ethmacc/CASA0021_GroupPrototypingPitch/Media/cardboard_prototype_1.jpg

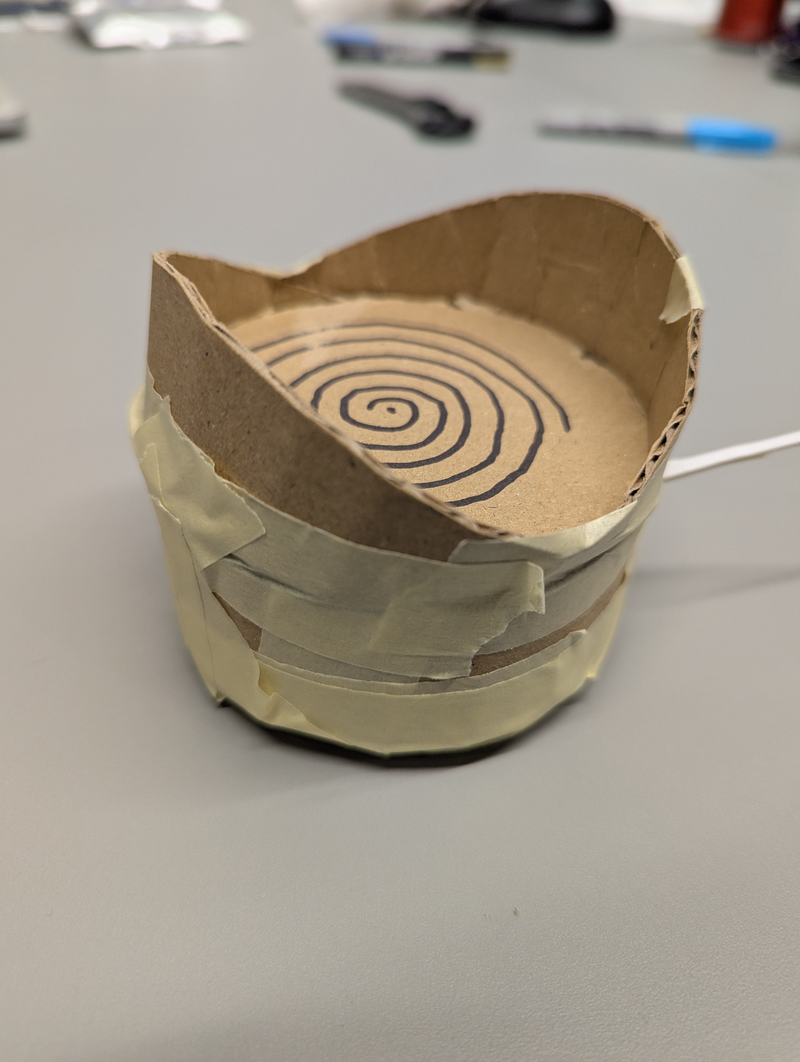
Media/cardboard_prototype_1.jpg
