ethmacc/CASA0021_GroupPrototypingPitch/Media/device_pair_1.jpg

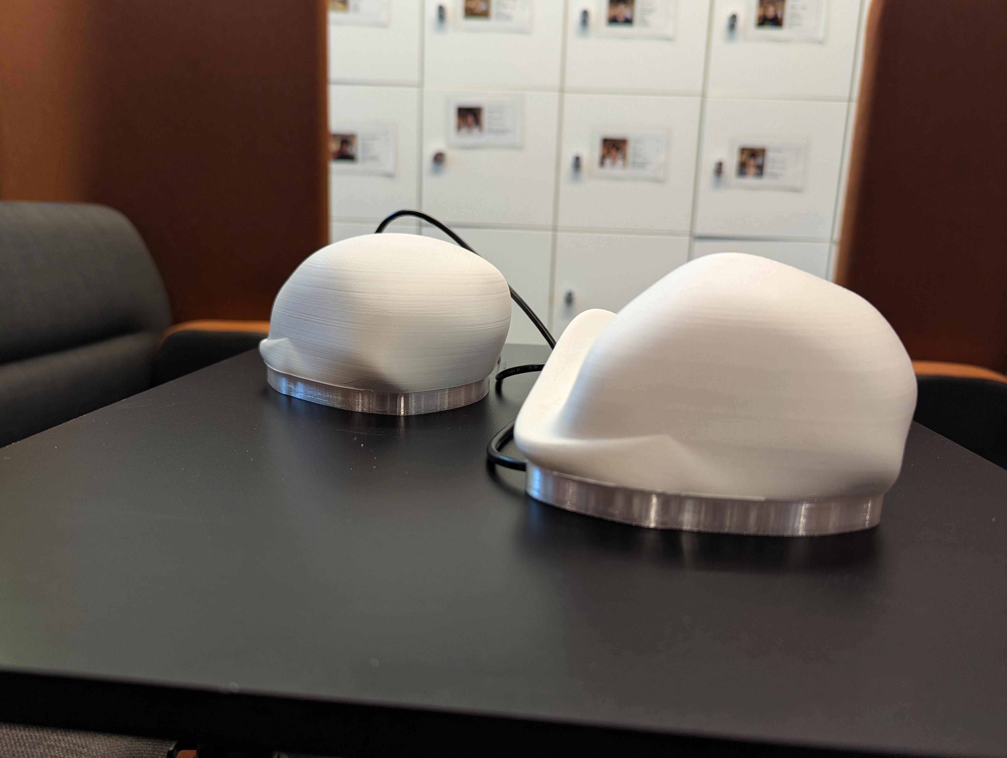
Media/device_pair_1.jpg
