ethmacc/CASA0021_GroupPrototypingPitch/Media/early_form_sketch.jpeg

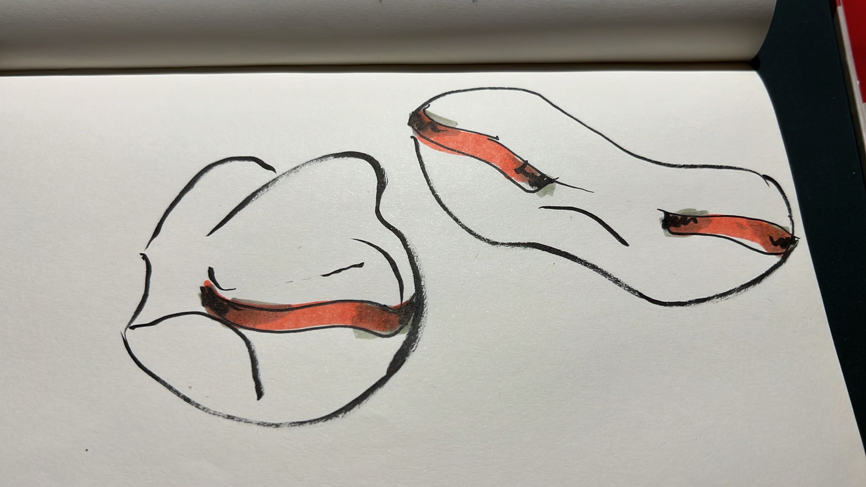
Media/early_form_sketch.jpeg
