ethmacc/CASA0021_GroupPrototypingPitch/Media/early_moon_sketch.jpeg

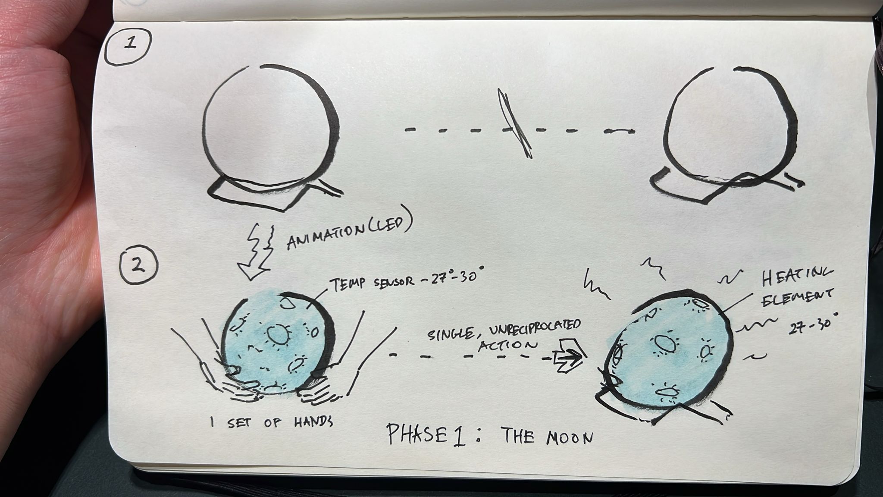
Media/early_moon_sketch.jpeg
