ethmacc/CASA0021_GroupPrototypingPitch/Media/early_sun_sketch.jpeg

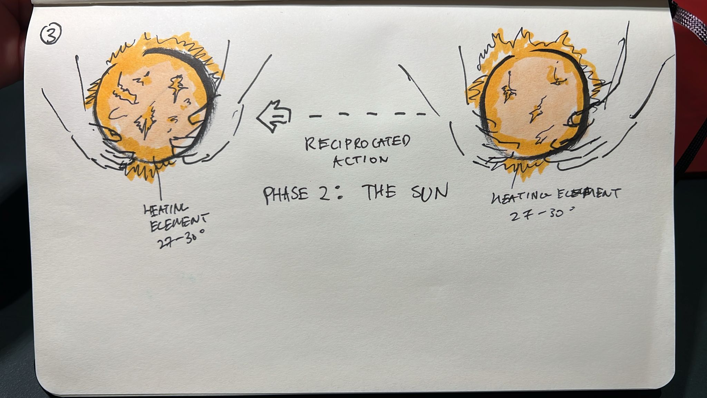
Media/early_sun_sketch.jpeg
