ethmacc/CASA0021_GroupPrototypingPitch/Media/early_watch_sketch.jpeg

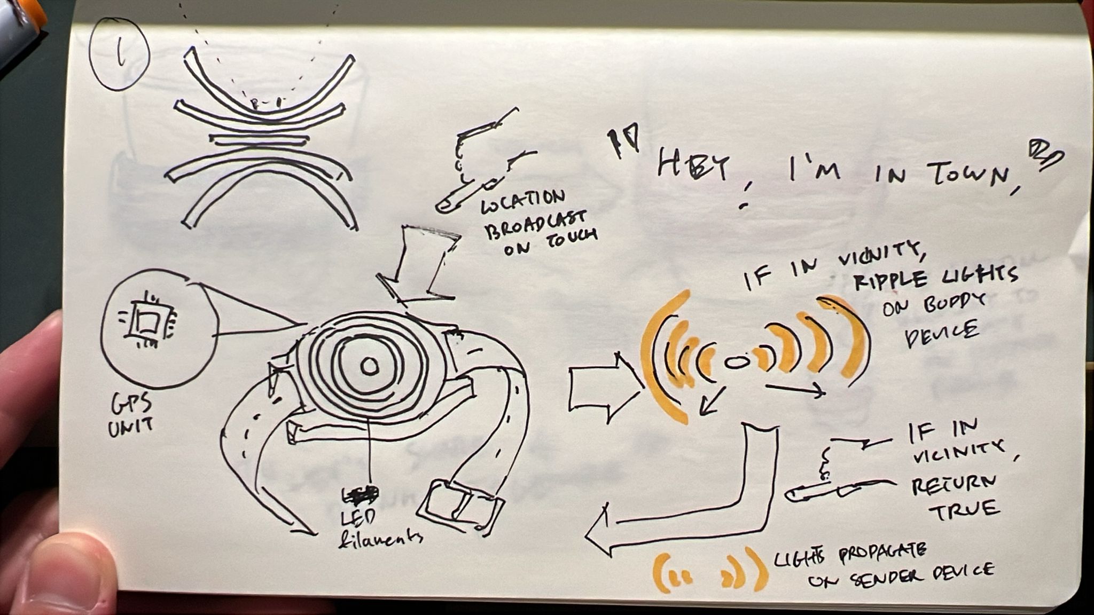
Media/early_watch_sketch.jpeg
