ethmacc/CASA0021_GroupPrototypingPitch/Media/electrical_diagram_1.jpeg

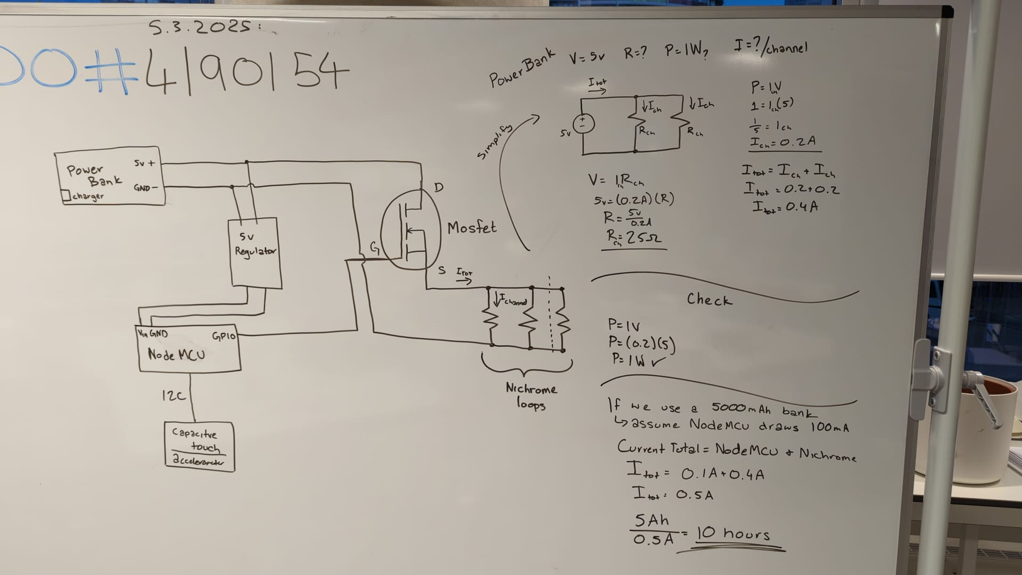
Media/electrical_diagram_1.jpeg
