ethmacc/CASA0021_GroupPrototypingPitch/Media/electrical_diagram_2.jpeg

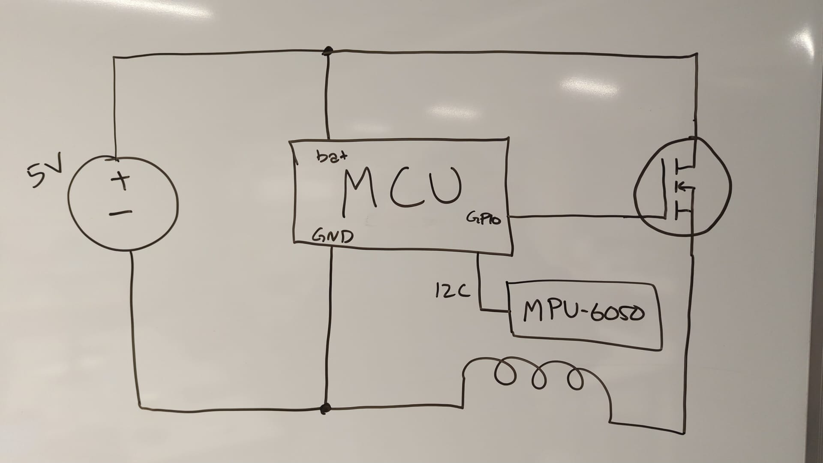
Media/electrical_diagram_2.jpeg
