ethmacc/CASA0021_GroupPrototypingPitch/Media/final_device_1.jpg

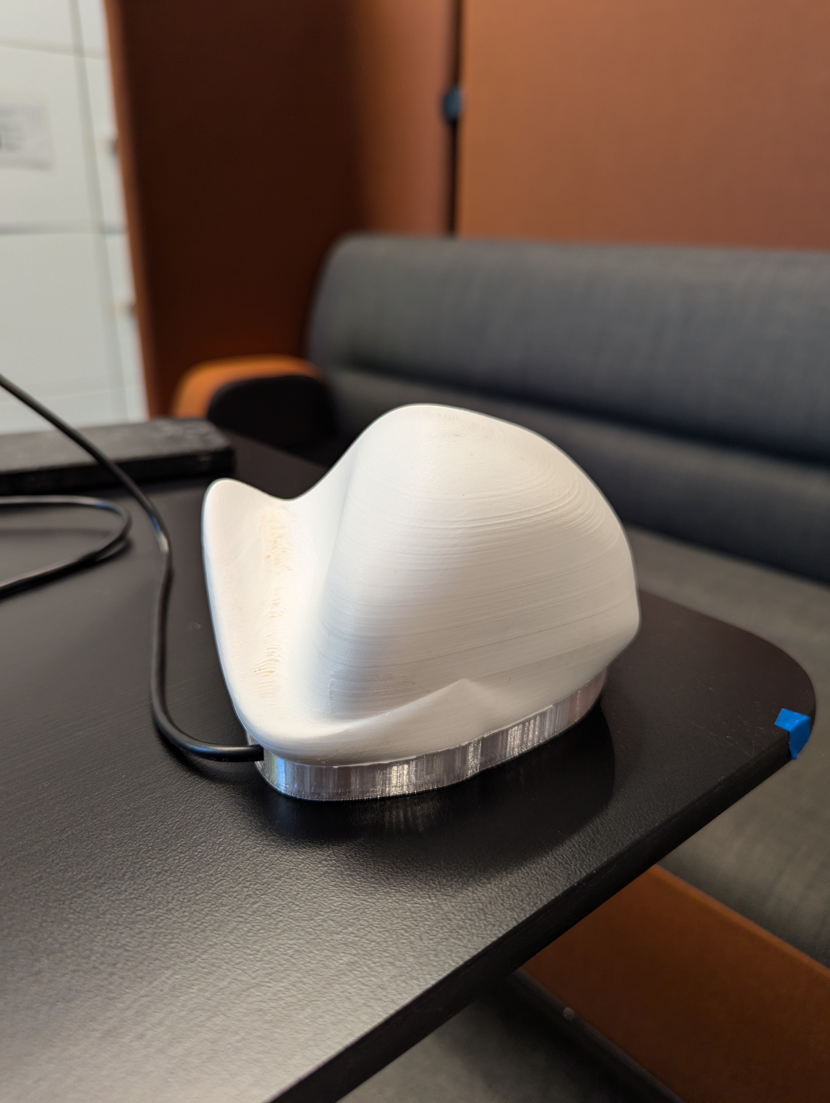
Media/final_device_1.jpg
