ethmacc/CASA0021_GroupPrototypingPitch/Media/lit_device_2.jpg

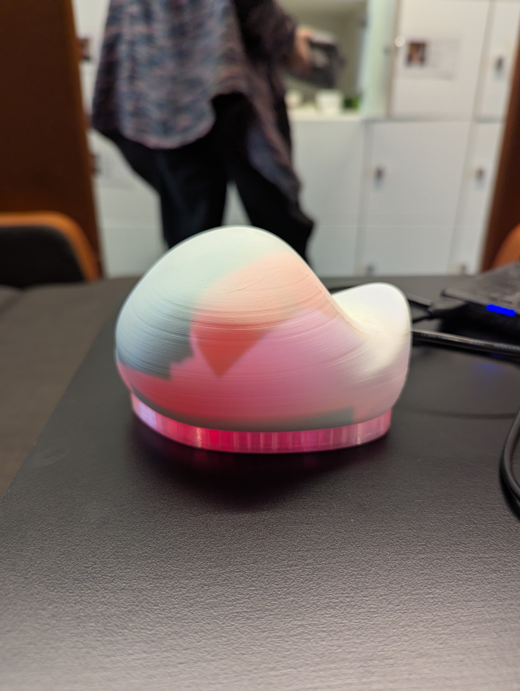
Media/lit_device_2.jpg
