ethmacc/CASA0021_GroupPrototypingPitch/Media/mug_model_1.jpeg

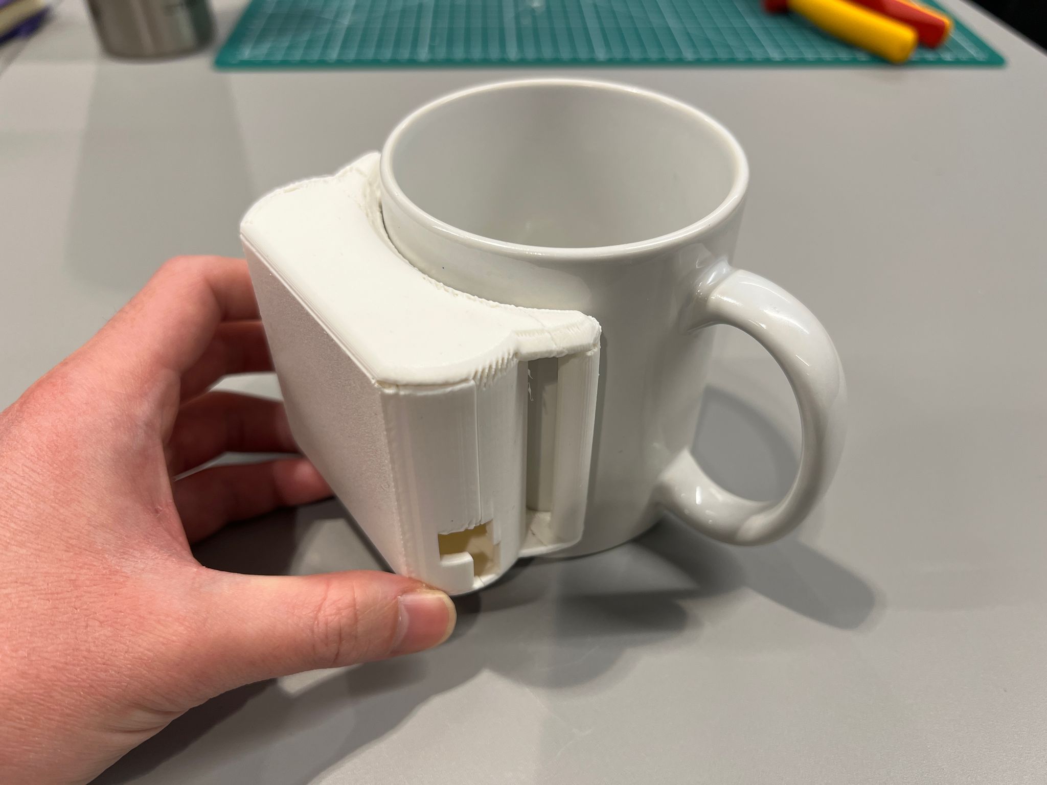
Media/mug_model_1.jpeg
