ethmacc/CASA0021_GroupPrototypingPitch/Media/mug_model_2.jpeg

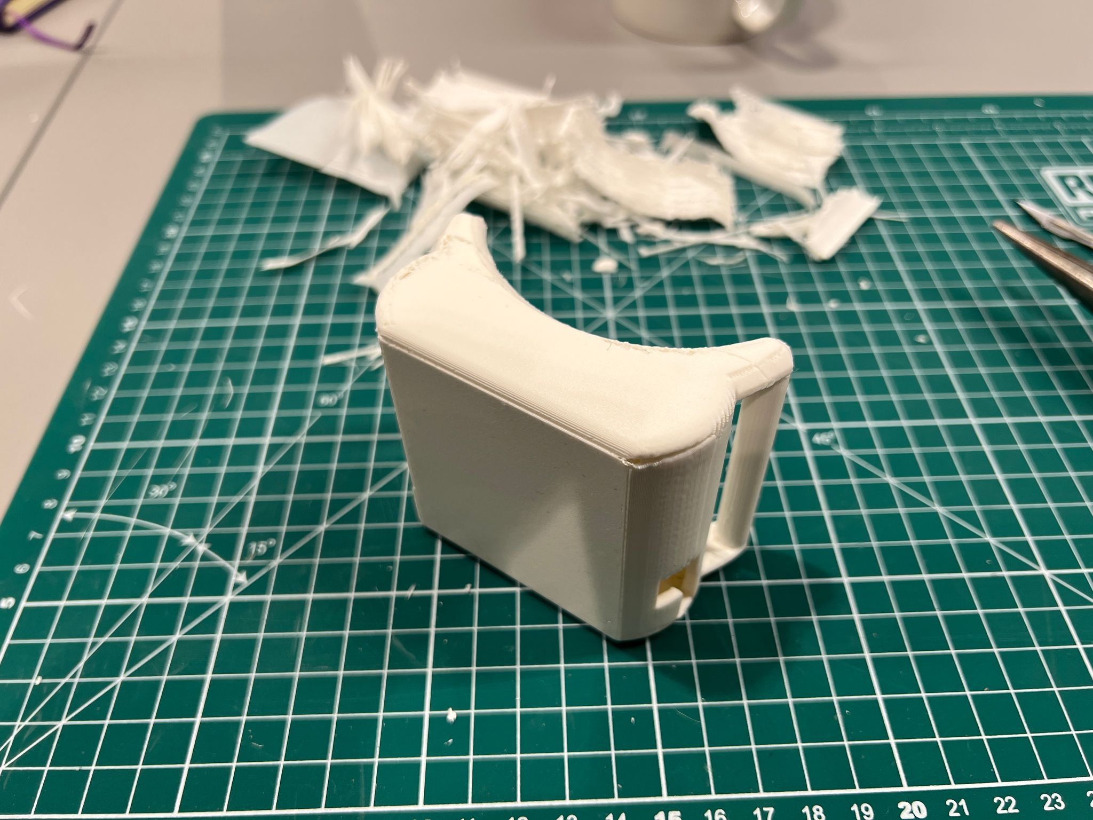
Media/mug_model_2.jpeg
