ethmacc/CASA0021_GroupPrototypingPitch/Media/renders/form_2025-Mar-22_11-45-30PM-000_CustomizedView218444586.png

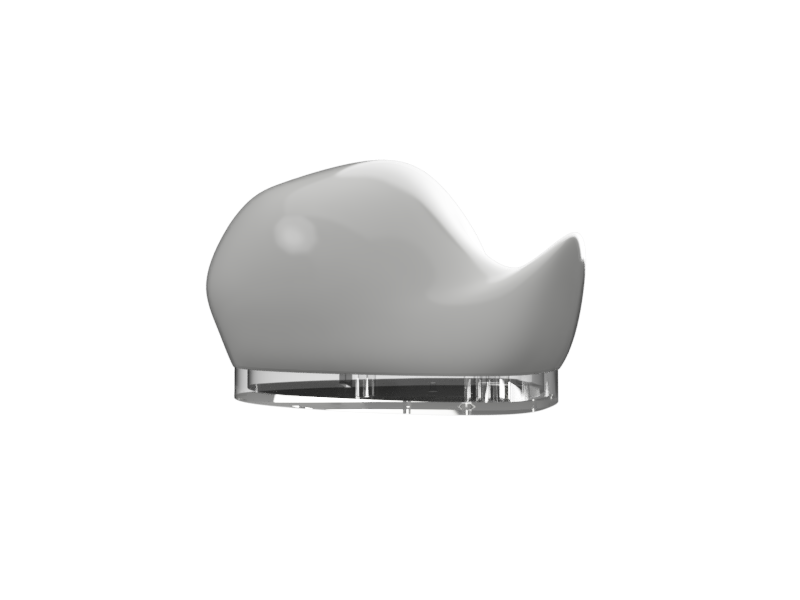
Media/renders/form_2025-Mar-22_11-45-30PM-000_CustomizedView218444586.png
