ethmacc/CASA0021_GroupPrototypingPitch/Media/renders/form_2025-Mar-22_11-54-31PM-000_CustomizedView12729331916.png

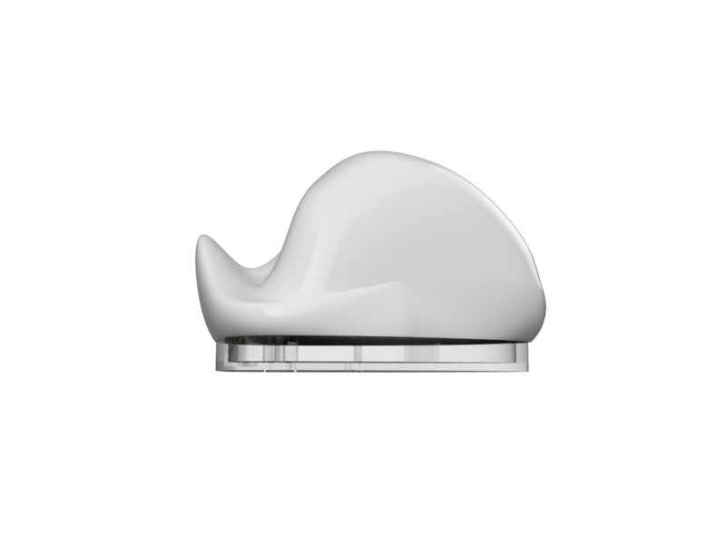
Media/renders/form_2025-Mar-22_11-54-31PM-000_CustomizedView12729331916.png
