ethmacc/CASA0021_GroupPrototypingPitch/Media/renders/form_2025-Mar-22_11-54-47PM-000_CustomizedView15713009611.png

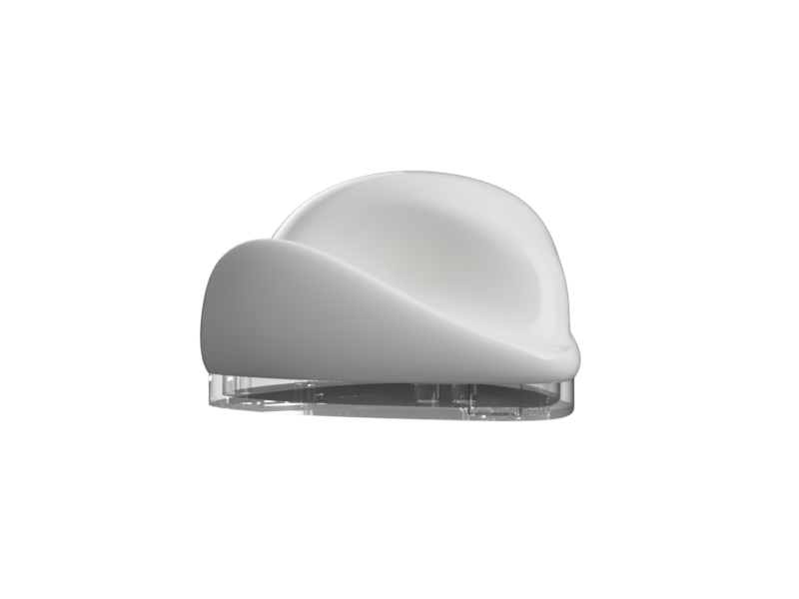
Media/renders/form_2025-Mar-22_11-54-47PM-000_CustomizedView15713009611.png
