ethmacc/CASA0021_GroupPrototypingPitch/Media/renders/proto1.png

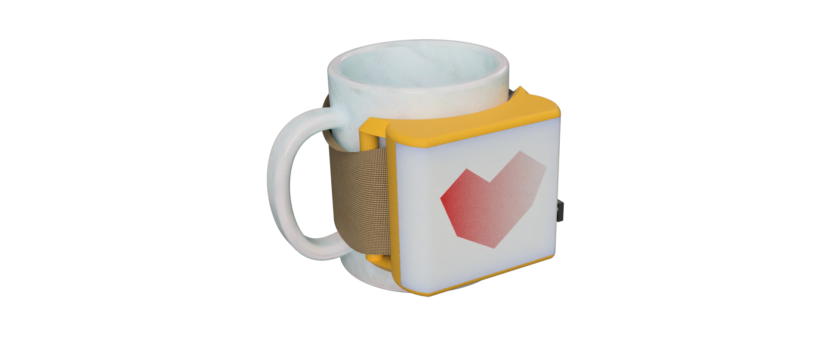
Media/renders/proto1.png
