ethmacc/CASA0021_GroupPrototypingPitch/Media/renders/proto2.png

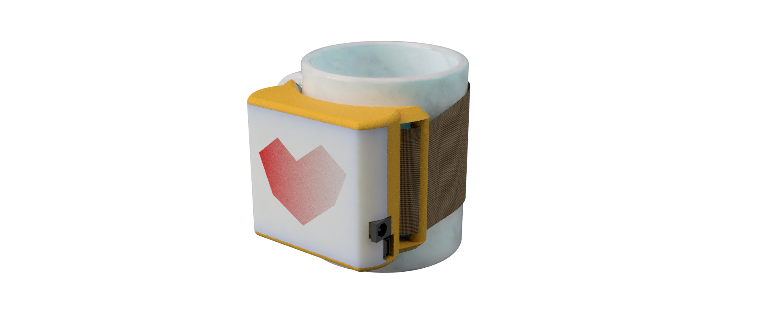
Media/renders/proto2.png
