ethmacc/CASA0021_GroupPrototypingPitch/Modeling/2D_models_textures/heart.png

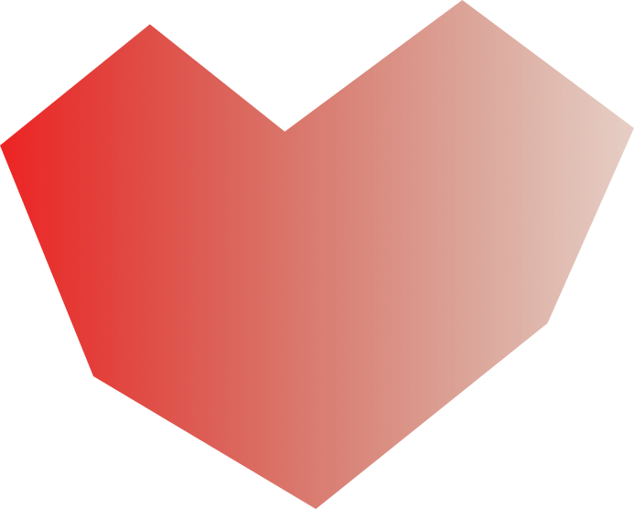
Modeling/2D_models_textures/heart.png
