ethmacc/CASA0021_GroupPrototypingPitch/Storyboard/IMG_5252.JPG

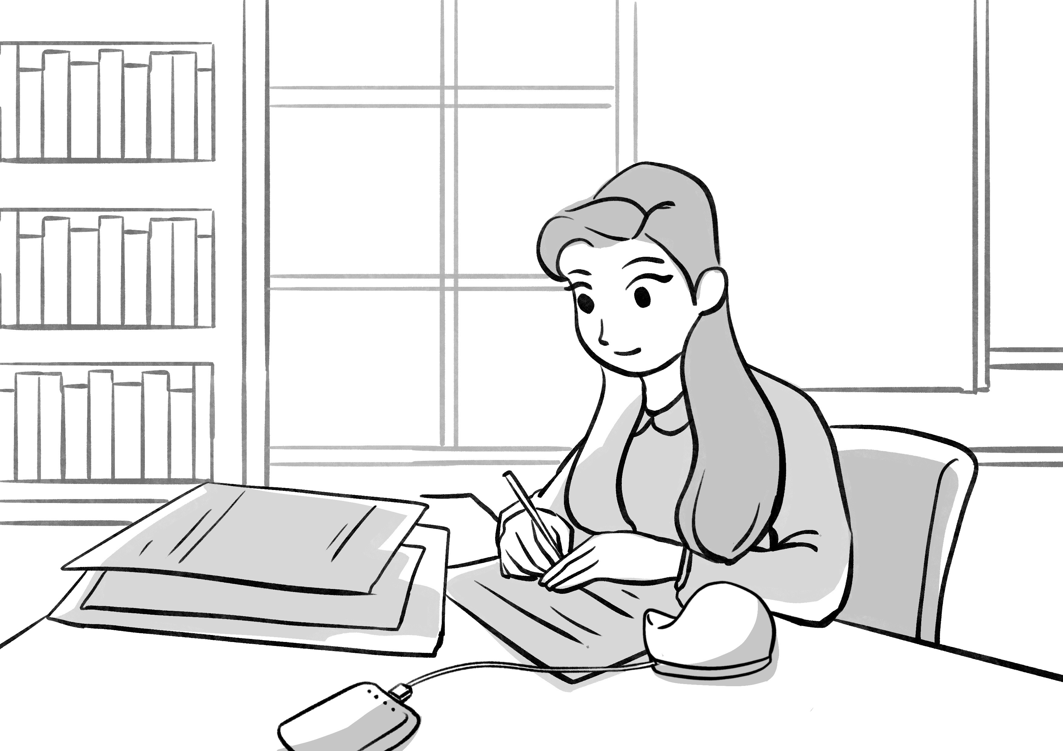
Storyboard/IMG_5252.JPG
