ethmacc/CASA0021_GroupPrototypingPitch/Storyboard/IMG_5253.JPG

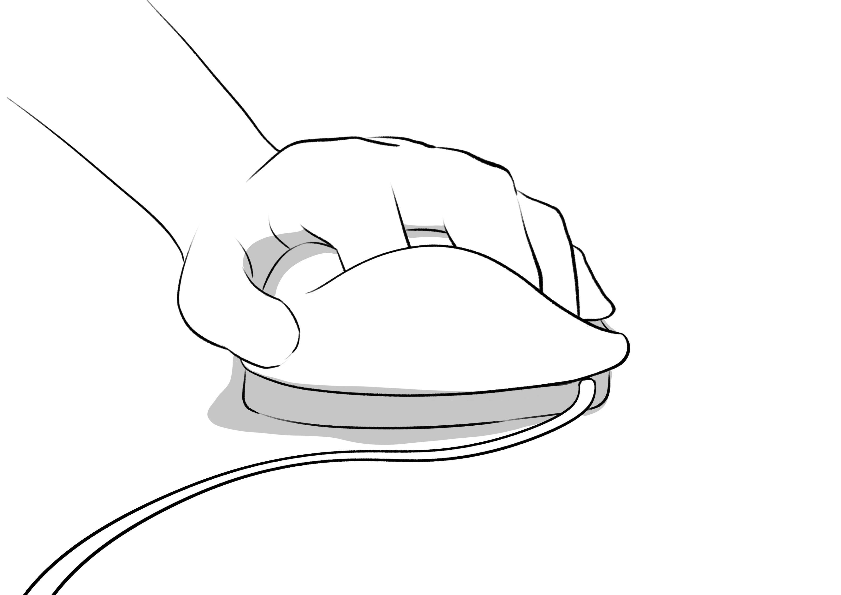
Storyboard/IMG_5253.JPG
