ethmacc/CASA0021_GroupPrototypingPitch/Storyboard/IMG_5254.JPG

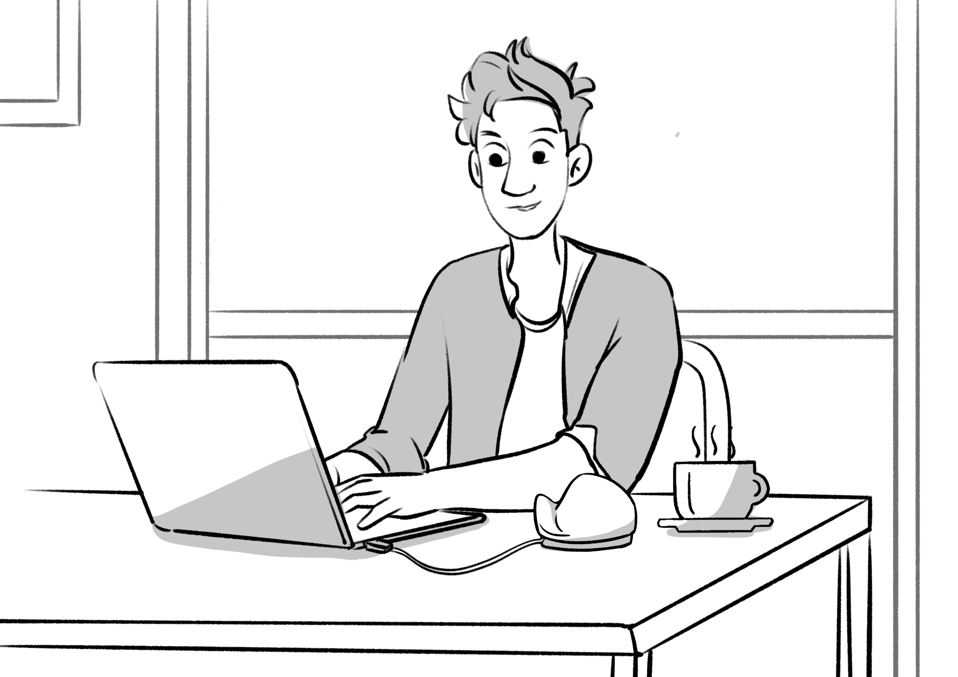
Storyboard/IMG_5254.JPG
