ethmacc/CASA0021_GroupPrototypingPitch/Storyboard/IMG_5255.JPG

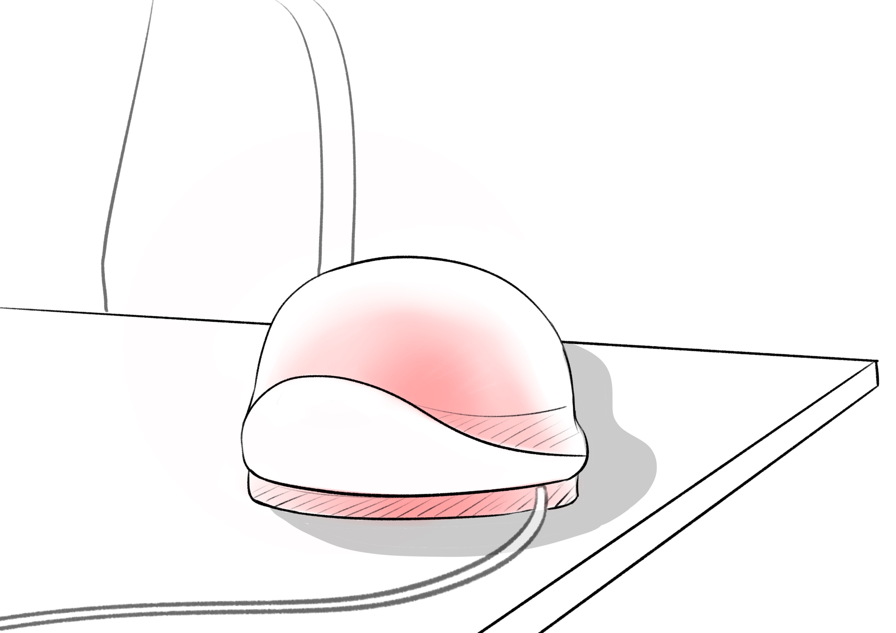
Storyboard/IMG_5255.JPG
