ethmacc/CASA0021_GroupPrototypingPitch/Storyboard/IMG_5256.JPG

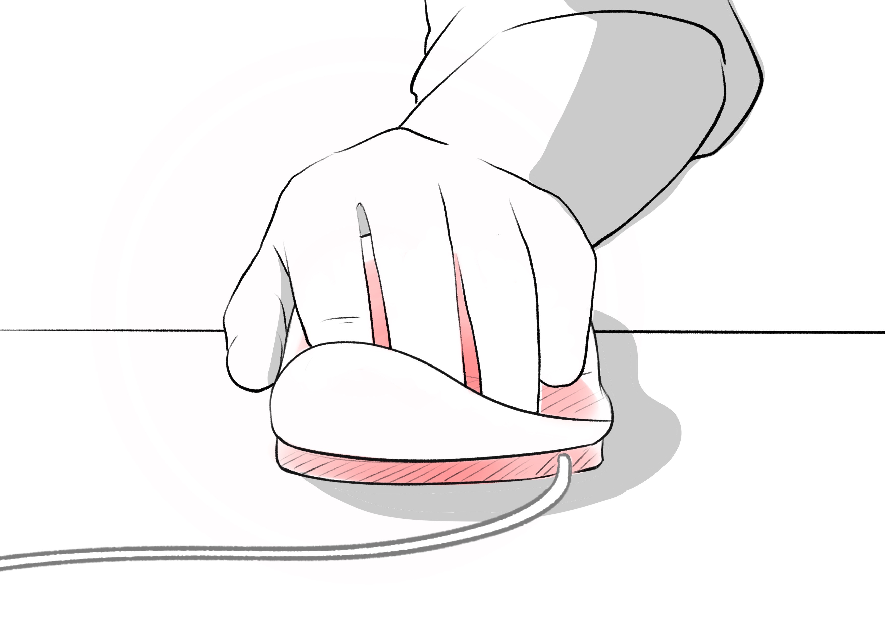
Storyboard/IMG_5256.JPG
