ethmacc/CASA0021_GroupPrototypingPitch/Storyboard/IMG_5257.JPG

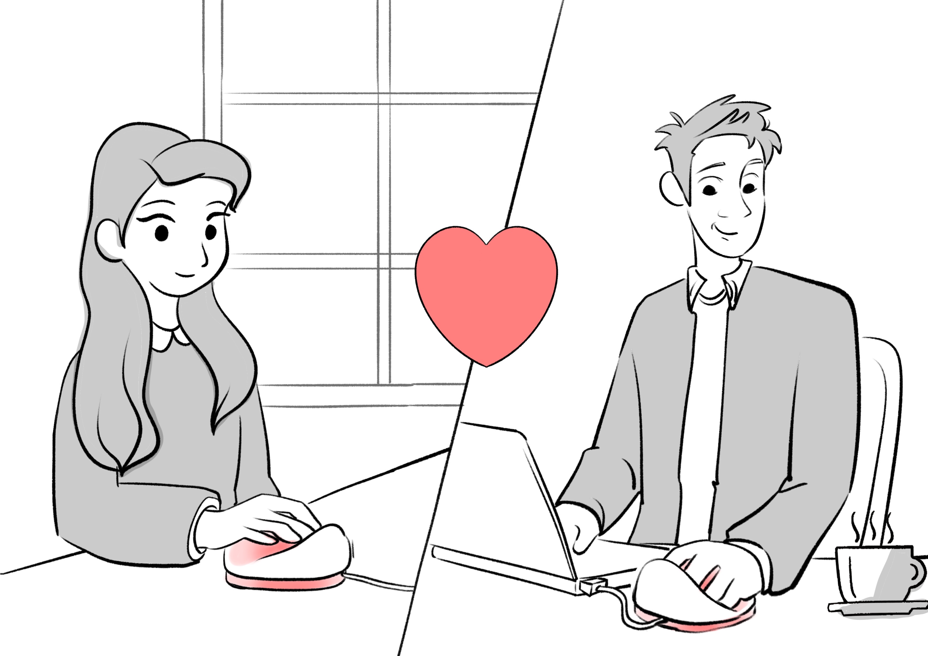
Storyboard/IMG_5257.JPG
