ethmacc/CASA0021_GroupPrototypingPitch/Storyboard/storyboard.PNG

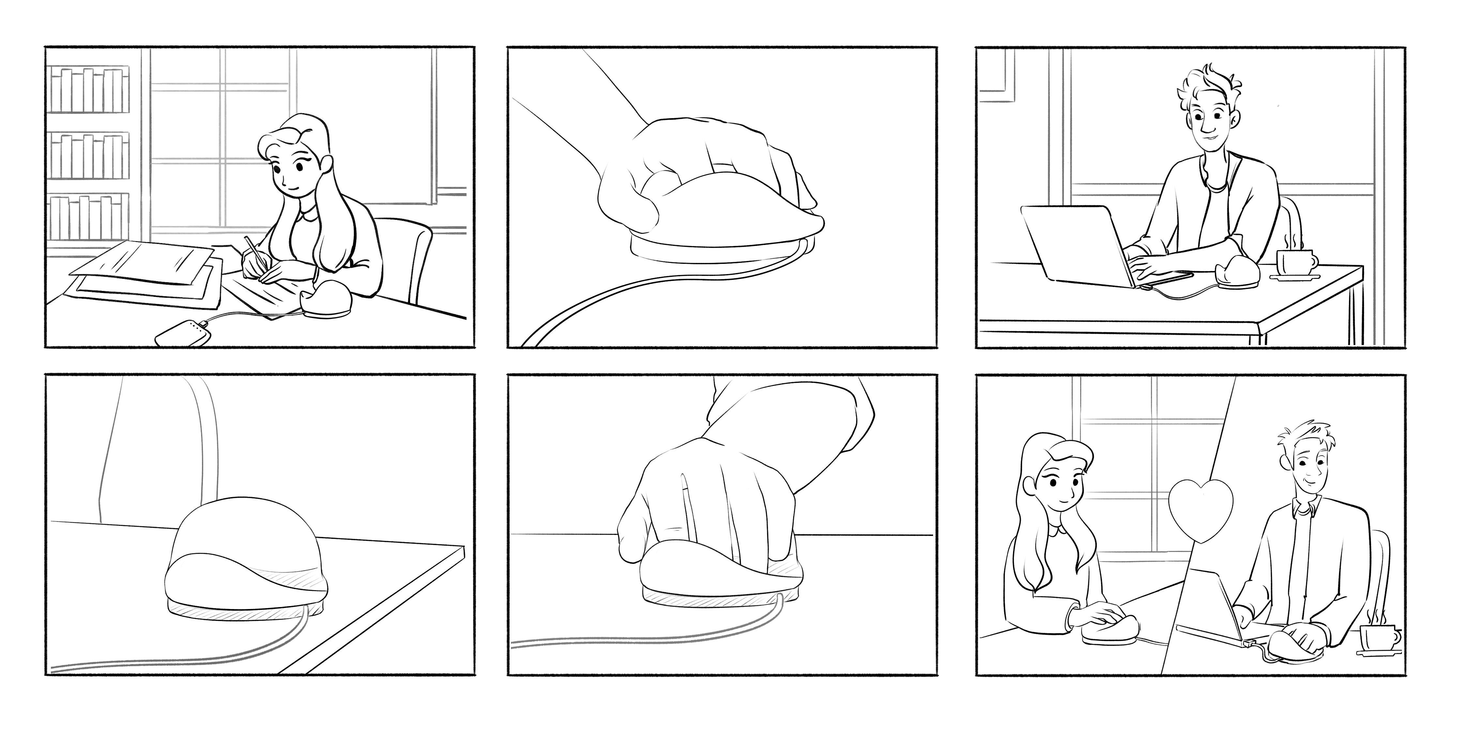
Storyboard/storyboard.PNG
