ethmacc/CASA0021_GroupPrototypingPitch/Storyboard/storyboard_color.PNG

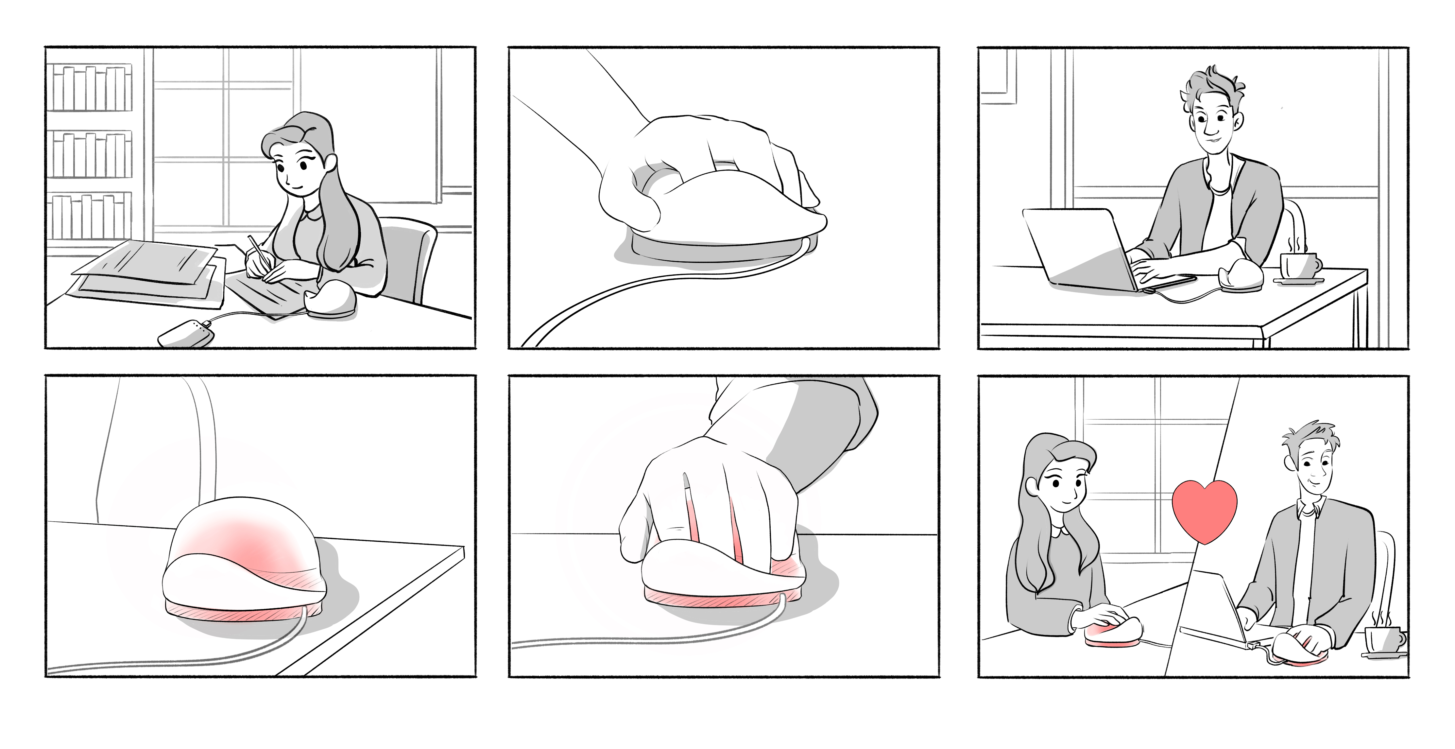
Storyboard/storyboard_color.PNG
