ethmacc/CASA0021_GroupPrototypingPitch/Media/blue_test_form_1.jpg

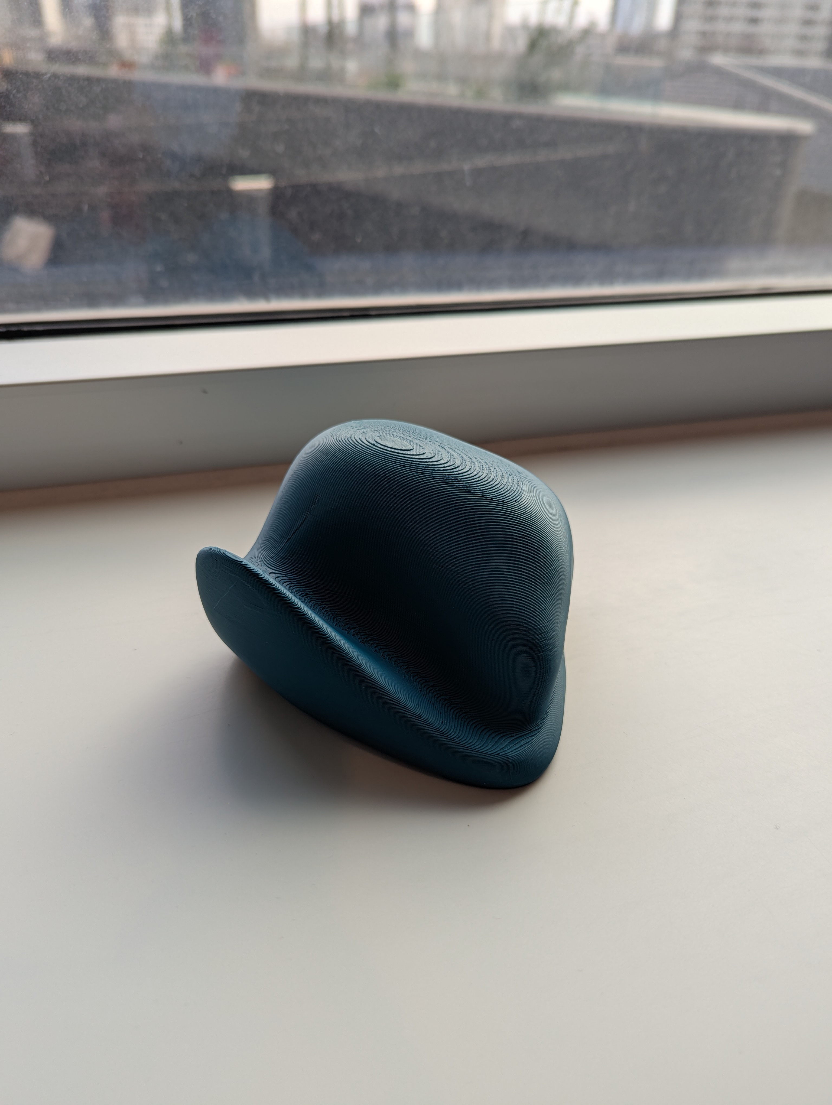
Media/blue_test_form_1.jpg
