ethmacc/CASA0021_GroupPrototypingPitch/Media/blue_test_form_2.jpg

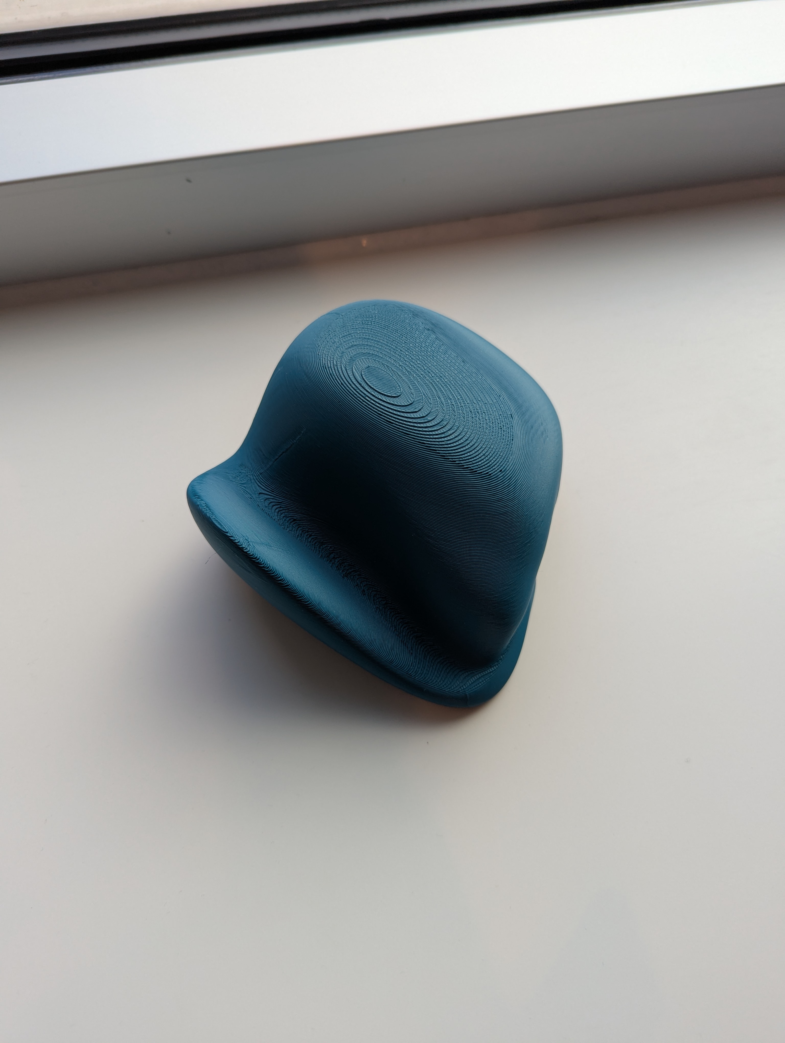
Media/blue_test_form_2.jpg
