ethmacc/CASA0021_GroupPrototypingPitch/Media/maroon_test_form_model_4.jpeg

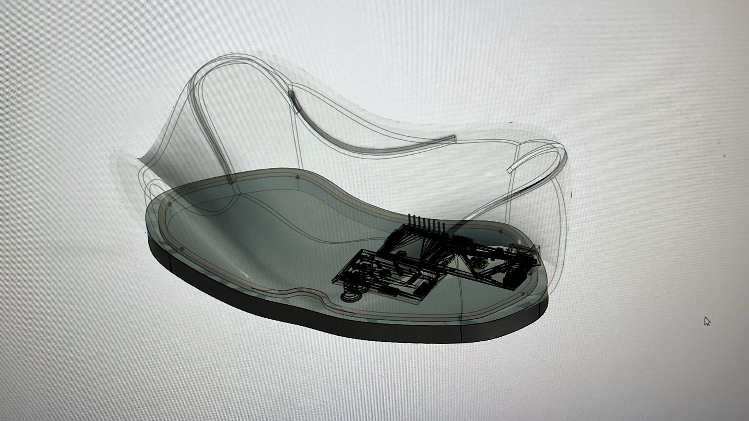
Media/maroon_test_form_model_4.jpeg
